eRadiofan/TMS6100-Multi-PHROM-Emulator-for-the-BBC-Micro/Firmware/Common/Src/ROMdata_TI99.c

// This is a dump of CD2325a and CD2326a combined. The index section is a binary tree!
#include "main.h"
#include "ROMdata.h"

const uint8_t phromData_TI99[DLEN_TI99] = {
  0x55, // Type: 0x55
  /* 0x0001 */  0x20, 0xb2, 0xf2, 0x4a, 0xa2, 0x20, 0x6d, 0x70, 0xad, 0x00, 0x62, 0x42, 0x8a, // Phrase 000: MORE -> 0x4642 L:0x04b6 R:0x0eb5
  /* 0x000e */  0x80, 0xb4, 0x90, 0x15, 0x00, 0x18, 0x00, 0x12, 0x3b, 0xbe, // Phrase 001: - -> 0x48dc L:0x09a8 R:0x0018
  /* 0x0018 */  0x80, 0x74, 0x00, 0x00, 0x00, 0x44, 0x00, 0x0a, 0x37, 0x3a, // Phrase 002: . -> 0x50ec R:0x0022
  /* 0x0022 */  0x80, 0x0c, 0x00, 0x00, 0x00, 0x00, 0x00, 0xc8, 0xc3, 0x62, // Phrase 003: 0 -> 0x13c3 
  /* 0x002c */  0x80, 0x8c, 0x00, 0x70, 0x00, 0x52, 0x00, 0x28, 0x90, 0xca, // Phrase 004: 1 -> 0x1409 L:0x000e R:0x004a
  /* 0x0036 */  0x80, 0x4c, 0x00, 0x00, 0x00, 0x02, 0x00, 0x28, 0x3a, 0x7c, // Phrase 005: 2 -> 0x145c R:0x0040
  /* 0x0040 */  0x80, 0xcc, 0x00, 0x00, 0x00, 0x00, 0x00, 0x28, 0x59, 0xb2, // Phrase 006: 3 -> 0x149a 
  /* 0x004a */  0x80, 0x2c, 0x00, 0x6c, 0x00, 0x2a, 0x00, 0x28, 0xe7, 0x52, // Phrase 007: 4 -> 0x14e7 L:0x0036 R:0x0054
  /* 0x0054 */  0x80, 0xac, 0x00, 0x00, 0x00, 0x7a, 0x00, 0xa8, 0x8c, 0xee, // Phrase 008: 5 -> 0x1531 R:0x005e
  /* 0x005e */  0x80, 0x6c, 0x00, 0x00, 0x00, 0x00, 0x00, 0xa8, 0x15, 0x02, // Phrase 009: 6 -> 0x15a8 
  /* 0x0068 */  0x80, 0xec, 0x00, 0x34, 0x00, 0x95, 0x00, 0xa8, 0x17, 0xf2, // Phrase 010: 7 -> 0x15e8 L:0x002c R:0x00a9
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
  0xa5, 0x4a, 0x4c, 0xd4, 0x8f, 0xde, 0x56, 0x77, 0x0d, 0xf1, 0xde, 0x7a, 0x5b, 0x42, 0xb5, 0x34,
  0x7b, 0xeb, 0x7d, 0x33, 0xe5, 0xf2, 0xf4, 0xa9, 0x57, 0x41, 0xc9, 0xab, 0x1c, 0xdb, 0x5e, 0xf7,
  0xba, 0xd7, 0xfd, 0x03, 0x00, 0x00,
  /* 0x3c4f KNOW, NO */
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
