eRadiofan/TMS6100-Multi-PHROM-Emulator-for-the-BBC-Micro/Firmware/Common/Src/ROMdata_StarWars.c

#include "main.h"
#include "ROMdata.h"

/*
0x0062,
0x019C,
0x0241,
0x02FC,
0x0436,
0x0577,
0x06C3,
0x0803,
0x08E0,
0x09D6,
0x0A59,
0x0B38,
0x0C4A,
0x0DBA,
0x0F31,
0x102E,
0x10A7,
0x11A4,
0x12C8,
0x14CD,
0x157D,
0x1747,
0x1810,
*/

#define toLE(x) x % 256, x / 256

const uint8_t phromData_StarWars[] = {
  0x00, 23, // Format type, No. of phrases: 23
  toLE(0x0030),
  toLE(0x016a),
  toLE(0x020f),
  toLE(0x02ca),
  toLE(0x0404),
  toLE(0x0545),
  toLE(0x0691),
  toLE(0x07D1),
  toLE(0x08AE),
  toLE(0x09a4),
  toLE(0x0a27),
  toLE(0x0b06),
  toLE(0x0c18),
  toLE(0x0d88),
  toLE(0x0eff),
  toLE(0x0ffc),
  toLE(0x1075),
  toLE(0x1172),
  toLE(0x1296),
  toLE(0x149b),
  toLE(0x154b),
  toLE(0x1715),
  toLE(0x17de),
  // "Use the force Luke"
  0x04, 0x00, 0x7A, 0x8A, 0x01, 0xC0, 0x4F, 0x33, 0x80, 0x68, 0x99, 0x50, 0x67, 0x8D, 0x9E, 0x95,
  0xB5, 0x5A, 0x9E, 0x8D, 0xA8, 0x86, 0x4F, 0x6E, 0x49, 0x34, 0xEE, 0x6A, 0xD1, 0xA8, 0x44, 0xC1,
  0x44, 0xB2, 0xF8, 0x92, 0x12, 0x78, 0x5F, 0x41, 0x6A, 0x4B, 0x8B, 0xEF, 0x7D, 0x27, 0x89, 0xCD,
  0x2B, 0xBE, 0x8F, 0x95, 0xA8, 0xD6, 0xAE, 0xF8, 0xDE, 0x57, 0x81, 0xD8, 0xBA, 0xE2, 0x07, 0x13,
  0x43, 0xA2, 0xED, 0x8A, 0x1F, 0xA5, 0x36, 0xBB, 0xAE, 0x2A, 0x41, 0x34, 0x66, 0x92, 0xD1, 0xB8,
  0x24, 0x55, 0xBB, 0x09, 0x5B, 0x92, 0x92, 0x4F, 0x67, 0x6A, 0xAC, 0x56, 0x0C, 0x10, 0x29, 0x8B,
  0x01, 0x0A, 0x46, 0x35, 0x40, 0x82, 0x6C, 0x0A, 0x08, 0x50, 0x98, 0x01, 0x1C, 0xB2, 0x2A, 0x80,
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
  0xD3, 0x96, 0x9A, 0xC8, 0xAC, 0x42, 0x4A, 0xDB, 0x5A, 0x24, 0xE7, 0x4A, 0x39, 0x65, 0xEB, 0x8D,
  0x42, 0x3B, 0xA4, 0xA4, 0xAD, 0x25, 0xB1, 0x48, 0x97, 0x8A, 0x80, 0x90, 0x62, 0x10, 0x10, 0x52,
  0xF6, 0x03, 0x03, 0xB4, 0xE0
};
