eRadiofan/TMS6100-Multi-PHROM-Emulator-for-the-BBC-Micro/Firmware/Common/Src/ROMdata_Acorn.c

// This is a dump of CM62024 the Acorn Speech PHROMA
#include "main.h"
#include "ROMdata.h"
/*
  PHROM Word list:

 Phrase address
 number (hex) Word

    0 0x0249  (0.125)
    1 0x0259  (0.25)
    2 0x026b  (TONE1)
    3 0x02a9  (TONE2)
    4 0x02e6  -DO
    5 0x02fd  -ED
    6 0x0327  -ING
    7 0x035f  -S
    8 0x037f  -TEEN
    9 0x03d9  -TH
   10 0x03f0  -TY
   11 0x0413  -Z
   12 0x0436  0
   13 0x04c6  00
   14 0x052d  000
   15 0x05c9  1
   16 0x0632  2
   17 0x0690  2-
   18 0x06d1  3
   19 0x073d  3-
   20 0x0787  4
   21 0x07f5  4-
   22 0x083f  5
   23 0x08b4  5-
   24 0x08e8  6
   25 0x0934  6-
   26 0x096d  7
   27 0x09c9  7-
   28 0x0a11  8
   29 0x0a44  8-
   30 0x0a70  9
   31 0x0afa  9-W
   32 0x0b5c  A
   33 0x0bb1  ACORN
   34 0x0c46  AFTER
   35 0x0cae  AGAIN
   36 0x0d40  AMOUNT
   37 0x0dbb  AN
   38 0x0e0f  AND
   39 0x0e87  ANOTHER
   40 0x0ef7  ANSWER
   41 0x0f6f  ANY
   42 0x0fc6  AVAILABLE
   43 0x1064  B
   44 0x10ba  BAD
   45 0x1134  BETWEEN
   46 0x11ad  BOTH
   47 0x11f2  BUTTON
   48 0x124c  C
   49 0x12a9  CASSETTE
   50 0x131d  CHARACTER
   51 0x1397  COMPLETE
   52 0x1403  COMPUTER
   53 0x147c  CORRECT
   54 0x14ef  D
   55 0x1537  DATA
   56 0x159b  DATE
   57 0x15e4  DO
   58 0x1624  DOLLAR
   59 0x167a  DONT
   60 0x16d3  DOWN
   61 0x1759  E
   62 0x1787  EACH
   63 0x17d0  ELEVEN
   64 0x184b  ENGAGED
   65 0x18f5  ENTER
   66 0x1957  ERROR
   67 0x19a4  ESCAPE
   68 0x1a1b  F
   69 0x1a5a  FEW
   70 0x1aa7  FILE
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
  /* 0x3f9a */  0x2d, // Z
  /* 0x3f9b */
  0x08, 0x38, 0x20, 0x4d, 0x02, 0x12, 0x08, 0xed, 0x05, 0x66, 0xee, 0x19, 0xa7, 0x34, 0x1b, 0xa8, 
  0x86, 0x55, 0xea, 0x91, 0x6c, 0x90, 0x9c, 0x9e, 0xb1, 0x4e, 0xb4, 0x71, 0x51, 0x66, 0xce, 0x3a,
  0xd1, 0xd0, 0x41, 0x65, 0x5d, 0xfb, 0x24, 0x43, 0x27, 0xb5, 0x77, 0xe3, 0x53, 0x8c, 0x10, 0x94,
  0x96, 0x8d, 0x4f, 0x35, 0x5c, 0x50, 0x46, 0xad, 0x3e, 0x4d, 0xb7, 0x41, 0x51, 0xb9, 0xe4, 0xf4,
  0xdd, 0x19, 0x67, 0xd6, 0x9c, 0x35, 0x74, 0x6d, 0x1c, 0x59, 0x8b, 0xcb, 0x38, 0xac, 0xb2, 0x69,
  0xb4, 0x36, 0x43, 0xd1, 0xcc, 0xa6, 0x53, 0x5a, 0x0c, 0x91, 0x8b, 0x56, 0xb4, 0x25, 0x33, 0x74,
  0xc5, 0xce, 0xae, 0x4e, 0xfe
  /* 0x4000 */
};
