eRadiofan/TMS6100-Multi-PHROM-Emulator-for-the-BBC-Micro/Firmware/Common/Src/ROMdata_VM61002.c

// This is a dump of VM61002 fitted in Acorn machines in the USA
#include "main.h"
#include "ROMdata.h"
/*
  PHROM Word list:

  Word or   Absolute
  word-part address
  number    (hex)    Word

  1         019E     ZERO
  2         01EB     FOUR
  3         0237     EIGHT
  4         026A     TWELVE
  5         02B3     TWENTY
  6         02FF     ONE
  7         0342     FIVE
  8         0395     NINE
  9         03ED     THIR-
  10        0425     HUNDRED
  11        047C     TWO
  12        04B3     SIX
  13        04E5     TEN
  14        051B     FIF-
  15        0541     THOUSAND
  16        05BA     THREE
  17        0606     SEVEN
  18        0650     ELEVEN
  19        06B8     TEEN-
  20        06EE     B
  21        0720     F
  22        075A     J
  23        079D     N
  24        07DD     R
  25        0809     V
  26        085D     ZEE
  27        0899     C
  28        08DB     G
  29        0919     K
  30        095A     O
  31        0988     S
  32        09B8     W
  33        0A1E     D
  34        0A52     H
  35        0A8D     L
  36        0ACC     P
  37        0B02     T
  38        0B3C     X
  39        0B75     A
  40        0BA3     E
  41        0BD9     I
  42        0C1B     M
  43        0C5A     Q
  44        0C8E     U
  45        0CCC     Y
  46        0D0E     ALPHA
  47        0D4F     ECHO
  48        0D91     DELTA
  49        0DE4     BRAVO
  50        0E41     FOXTROT
  51        0EB0     CHARLIE
  52        0F01     GOLF
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
  0x57, 0xdf, 0x54, 0x5b, 0x85, 0xbe, 0xd9, 0xe3, 0x5c, 0xc6, 0xd6, 0x6d, 0xb1, 0xa5, 0xbf, 0x99,
  0x5b, 0x3b, 0x5a, 0x30, 0x09, 0xaf, 0x2f, 0xed, 0xec, 0x31, 0xc4, 0x5c, 0xbe, 0xd6, 0x33, 0xdd,
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
};
