eRadiofan/TMS6100-Multi-PHROM-Emulator-for-the-BBC-Micro/Firmware/Common/Src/ROMdata_VM61004.c

// This is a dump of VM61004, non-indexed PHROM containing military radio phrases
#include "main.h"
#include "ROMdata.h"
/*
   PHROM Word list:

   Absolute
    address
     (hex)  Word
         0  Alpha
        64  Bravo
        BC  Charlie
       11E  Delta
       171  Echo
       1B3  Foxtrot
       248  Golf
       280  Hotel
       2F6  India
       356  Juliet
       3BC  Kilo
       409  Lima
       44C  Mike
       48E  November
       52A  Oscar
       587  Papa
       5C9  Quebec
       610  Romeo
       670  Sierra
       706  Tango
       77D  Uniform
       7FB  Victor
       86E  Whisky
       8C7  Xray
       93B  Zulu
       984  Affirmative
       A38  Negative
       ACF  Mayday
       B74  Warning
       C07  Icing
       C78  Danger
       D0B  Emergency
       DD2  Roger
       E50  Hertz
       E8D  (Pause)
       E96  Security
       F13  Target
       F6E  Vectors
       FE6  Light
      103D  Front
      1098  Way
      10DA  Glide
      115E  Open
      11C2  Lights
      1221  On
      1287  Gun dish
      130A  ArdNav
      13B9  Select
      1420  Filed
      14A5  MIG
      1511  Alert
      1579  Zone
      15FD  Terminal
      167E  Cancel
      16EB  Radios
      178E  Speed
      1800  Knots
      1868  Expect
      18D6  Action
      193C  Radio
      19AA  Power
      1A07  Path
      1A5F  Information
      1B09  True
      1B52  Pressure
      1BBF  Check
      1BF6  Decrease
      1C63  Advise
      1CED  You
      1D27  Half
      1D7E  Error
      1DDA  Call
      1E31  Wrong
      1E91  No
      1EEA  Immediately
      1FA3  Final
      200F  Please
      205A  Start
      20B6  Course
      2102  RADAR
      2181  Plan
      21EE  Target
      225B  Windows
      22F3  Watch
      2336  Use (s)
      2381  Turn
      23CE  Traffic
      2435  Tech
      248A  Slow
      24F9  Release
      256D  Key
      25A8  Ignition
      2639  Degree
      26A4  Grain
      26F9  Repair
      277C  Cancel
      2806  Verify
      28A0  Ready
      28FA  Use (z)
      2976  Out
      29BF  Other
      2A25  Oil
      2A78  Off
      2AC6  Mirror
      2B26  Rate
      2B93  Mixture
      2C16  Much
      2C6E  Rate
      2CD0  Is
      2D28  Caution
      2D97  Below
      2E13  Cylinder
      2E90  Contact
      2F0A  And
      2F51  Fuel
      2FA8  For
      2FE2  Sequence
      3068  Side
      30C3  Slow
      3119  To
      3148  Rich
      31B6  Pumps
      320C  Level
      3273  Lower
      32E5  Rear
      3364  Hold
      33C9  Long
      3435  Level
      34AE  Left
      350F  Right
      356F  Open
      35C9  Stray
      3659  Closed
      36E2  Evacuate
      379A  Failure
      3807  Service
      3881  Abort
      3902  Identify
      3999  Too low
      3A2F  Centre
      3AA9  Area
      3B09  Base
      3B45  Control
      3BBB  Measured
      3C41  The (ee)
      3C74  The (uh)
      3C95  Vacuum
      3D13  Abeam
*/

const uint8_t PHROMdata_Mil[DLEN_Milit] = {
  /* 0x0000 */
  0x63, 0xa9, 0x21, 0xb4, 0x3c, 0x16, 0xaf, 0xb6, 0x84, 0xd2, 0x0a, 0x5f, 0xb3, 0xaa, 0xe2, 0xda, 
  0x32, 0xf4, 0xcd, 0x2a, 0x93, 0xdf, 0x28, 0xd7, 0x27, 0xab, 0xc8, 0xe2, 0x5b, 0x93, 0x57, 0xaf,
  0xb2, 0xd0, 0x1b, 0x0b, 0xee, 0xb2, 0xca, 0x24, 0xae, 0xc3, 0x28, 0x4b, 0xa9, 0x0b, 0xaf, 0x0e,
  0x13, 0x47, 0x02, 0xa8, 0xa6, 0x4c, 0x00, 0x4d, 0x57, 0x08, 0xa0, 0x99, 0x0c, 0x01, 0x74, 0xed,
  0xb1, 0xea, 0x22, 0xba, 0xd4, 0xa9, 0xcd, 0xaa, 0x2b, 0xef, 0xd6, 0xe0, 0xbd, 0x6b, 0x69, 0xac,
  0x5a, 0x83, 0xf7, 0xae, 0xb3, 0xb1, 0x6a, 0x0b, 0xde, 0x32, 0xf6, 0xa2, 0x3a, 0xc2, 0x79, 0x73,
  0xbd, 0xf2, 0xfd,
  0xff,
  /* 0x0064 */
  0x02, 0x10, 0x2c, 0x34, 0xb4, 0x46, 0xaf, 0xc8, 0x8a, 0xbd, 0xd4, 0x84, 0xa9, 0xe6, 0x2d, 0xfc, 
  0x46, 0x1d, 0x7b, 0x48, 0x87, 0x2a, 0x5f, 0x55, 0x76, 0x13, 0xe9, 0xba, 0x7a, 0x97, 0xbb, 0x9c,
  0x55, 0x69, 0xa3, 0xab, 0x48, 0xd7, 0xd5, 0xb1, 0x0f, 0x63, 0xf7, 0xa1, 0xe6, 0x2a, 0x3b, 0x8e,
  0x65, 0x0c, 0xa9, 0x52, 0x55, 0x56, 0x8d, 0xb6, 0x92, 0x6a, 0x77, 0xf1, 0xbb, 0xc6, 0x86, 0xb2,
  0x3a, 0x44, 0xfd, 0x9c, 0xdb, 0x52, 0x48, 0xd7, 0x38, 0xb9, 0xef, 0x7b, 0xdd, 0xc3, 0xee, 0x7d,
  0x67, 0xb0, 0xf4, 0x89, 0x67, 0xbc, 0xfe,
  0x1f,
  /* 0x00bc */
  0x06, 0xd8, 0x2d, 0x2c, 0x01, 0x33, 0xb7, 0x67, 0xa0, 0xc5, 0xc5, 0x8d, 0xc8, 0xb2, 0xb7, 0x96, 
  0x17, 0xbf, 0x26, 0x87, 0xf9, 0x5a, 0x91, 0xf3, 0xb0, 0x1f, 0x75, 0x19, 0x45, 0xce, 0xcd, 0x71,
  0xd4, 0x65, 0x54, 0x39, 0x8e, 0xda, 0x71, 0xb6, 0xd1, 0xc5, 0x30, 0xe9, 0x6e, 0x69, 0xcb, 0x5c,
  0x51, 0x8f, 0x15, 0x66, 0x49, 0xfb, 0x80, 0x31, 0xa2, 0xe6, 0x7d, 0x9d, 0x55, 0xb6, 0x59, 0xd8,
  0xea, 0x71, 0x0f, 0xde, 0xca, 0xe5, 0x9b, 0xc7, 0xd3, 0x65, 0x92, 0x55, 0x6c, 0x2e, 0xef, 0x30,
  0x49, 0x92, 0xb1, 0x3a, 0xbd, 0xc3, 0x04, 0x72, 0xe7, 0xe6, 0xf0, 0x75, 0xeb, 0xa8, 0x93, 0xab,
  0xff,
  0x1f,
  /* 0x011e */
  0x0a, 0x28, 0x30, 0x6c, 0xad, 0xc3, 0xa7, 0xaa, 0x70, 0xd7, 0xd5, 0x76, 0x5d, 0x22, 0xee, 0x5b, 
  0x57, 0xd9, 0xf9, 0xb8, 0xa6, 0x6d, 0x59, 0x65, 0x16, 0x9b, 0xa1, 0xde, 0x7b, 0xd5, 0x99, 0x6d,
  0xa5, 0x58, 0xde, 0xd5, 0x64, 0x11, 0x5d, 0xc2, 0x69, 0xca, 0x30, 0x25, 0x5b, 0x85, 0x32, 0x21,
  0x40, 0x96, 0x26, 0x0e, 0x58, 0x4a, 0x33, 0x00, 0x4b, 0xb5, 0xad, 0xae, 0x9a, 0xf0, 0x30, 0xdf,
  0xb2, 0xc7, 0x31, 0x35, 0x55, 0xe9, 0x21, 0x5d, 0xfb, 0x34, 0xf6, 0xaa, 0xc6, 0x3c, 0xa5, 0x73,
  0x3f, 0xfe,
  0x1f,
  /* 0x0171 */
  0x2b, 0x6f, 0xb1, 0xd9, 0xd3, 0x36, 0xdf, 0xf6, 0x36, 0xb7, 0x26, 0x85, 0x08, 0xe5, 0x2e, 0x22, 
  0x1b, 0x20, 0x00, 0x25, 0xac, 0x2a, 0x20, 0xcf, 0xd3, 0x52, 0x45, 0x53, 0x6a, 0xa9, 0x9e, 0x4f,
  0x9b, 0x54, 0x47, 0xb9, 0xe4, 0xdf, 0xc3, 0x1c, 0xc6, 0x98, 0x45, 0x65, 0xbb, 0x78, 0x9f, 0xcb,
  0x5c, 0xd2, 0xea, 0x43, 0x67, 0xb0, 0xe5, 0xcd, 0x7b, 0x38, 0x9d, 0xad, 0x2c, 0x15, 0x37, 0xf1,
  0xfc,
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
}; // 149 phrases
