eRadiofan/TMS6100-Multi-PHROM-Emulator-for-the-BBC-Micro/Firmware/Common/Src/ROMdata_VM71003A.c

// This is a dump of VM71003A (female clock)
#include "main.h"
#include "ROMdata.h"
/*
Word or   Absolute
word-part address
number    (hex)    Word

1         0048     THE
2         006A     TIME
3         00F7     IS
4         015C     AM
5         0203     PM
6         0283     OH
7         02BF     O'CLOCK
8         031D     ONE
9         0383     TWO
10        03B6     THREE
11        041E     FOUR
12        047B     FIVE
13        04F9     SIX
14        052C     SEVEN
15        0584     EIGHT
16        05CB     NINE
17        063F     TEN
18        06A6     ELEVEN
19        0733     TWELVE
20        07AE     THIRTEEN
21        084E     FOURTEEN
22        08C5     FIFTEEN
23        0958     SIXTEEN
24        09F0     SEVENTEEN
25        0AAB     EIGHTEEN
26        0B46     NINETEEN
27        0C08     TWENTY
28        0C71     THIRTY
29        0CDC     FOURTY
30        0D47     FIFTY
31        0DA8     GOOD
32        0DC7     MORNING
33        0E52     AFTERNOON
34        0EF3     EVENING
35        0F6C     (0.25)
*/

const uint8_t PHROMdata_Clock[DLEN_CLOCK] = {
  0x00, 0x23, // Format type, No. of phrases: 35
  0x48, 0x00, // Phrase 000 @ 0x0048
  0x6a, 0x00, // Phrase 001 @ 0x006a
  0xf7, 0x00, // Phrase 002 @ 0x00f7
  0x5c, 0x01, // Phrase 003 @ 0x015c
  0x03, 0x02, // Phrase 004 @ 0x0203
  0x83, 0x02, // Phrase 005 @ 0x0283
  0xbf, 0x02, // Phrase 006 @ 0x02bf
  0x1d, 0x03, // Phrase 007 @ 0x031d
  0x83, 0x03, // Phrase 008 @ 0x0383
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
  0xab, 0x69, 0xda, 0x2b, 0x18, 0x9e, 0x3d, 0x37, 0x69, 0x9d, 0xa8, 0x07, 0x71, 0x9f, 0xa0, 0xbd,
  0xa2, 0x16, 0xd5, 0x7c, 0x54, 0xf6, 0x88, 0x6b, 0x54, 0x8b, 0x34, 0x49, 0x2d, 0x29, 0x49, 0x3c,
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
};
