eRadiofan/TMS6100-Multi-PHROM-Emulator-for-the-BBC-Micro/BASIC2/SPHRASE.bas

   10 REM >SPHRASE
   20
   30 PROCasm
   40 REM Reset 5220
   50 Y%=&70:CALL CMD
   60 CLS
   70 PROCPHRASE_I(15,208)
   80 PROCSETADDR(0,0)
   90 RTPE%=FNREAD
  100 PROCSETADDR(10,1)
  110 STW%=FNREAD
  120
  130 IF RTPE%=&AA THEN PRINT "PHROM ID (0,4,10,15)";
  140 IF RTPE%<>&AA AND STW%=232 THEN PRINT "PHROM ID (0,2,4,10,15)";
  150 IF RTPE%<>&AA AND STW%<>232 THEN PRINT "PHROM ID (0,2,4,15)";
  160 INPUT RN%
  170 BN% = 1
  180 IF RN% = 2 THEN BN%=0:MAX%=148:PROCINITDATA
  190 IF RN% = 0 AND RTPE%=&AA THEN PROCTI99INDEX:BN%=0:MAX%=373
  200 IF RN% = 0 AND RTPE% <> &AA THEN MAX%=206
  210 IF RN% = 10 MAX%=23
  220 IF RN% = 15 THEN BN% = 32:MAX% = 260:PRINT "Phrase Acorn = 129"
  230 IF RN% = 4 THEN MAX% = 35
  240 LAST% = 1
  250 PRINT"<RETURN> = Previous, -1 = All"
  260 REPEAT
  270   PRINT "Phrase number (1-";MAX%;")";
  280   INPUT PN%
  290   IF (PN% = 0) THEN PN% = LAST%
  300   IF PN% = -1 THEN PROCALL(RN%,BN%,MAX%-1) ELSE PROCPHRASE(RN%,BN%+PN%-1)
  310   LAST% = PN%
  320 UNTIL 0
  330
  340 DEFPROCPHRASE(RN%,PN%)
  350 AN% = -1
  360 IF RTPE%=&AA AND RN%=0 THEN AN%=IDX99%(PN%)
  370 IF RN%=2 THEN AN%=IDXDATA%(PN%)
  380 REM PRINT PN%, ~AN%
  390 IF (AN% > &4000) THEN RN%=RN%+1:AN%=AN%-&4000
  400 IF AN% >= 0 THEN PROCSETADDR(RN%,AN%):PROCSPEAK ELSE PROCPHRASE_D(RN%,PN%)
  410 ENDPROC
  420
  430 DEF PROCALL(RN%,BN%,MAX%)
  440 FOR I% = 0 TO MAX%
  450   PRINT "Phrase ";I%+1
  460   PROCPHRASE(RN%,BN%+I%)
  470   PROCWAITEOS
  480   FOR J%=0 TO 1000:NEXT
  490 NEXT
  500 ENDPROC
  510
  520 DEF FNREVERSE(A%)
  530 =USR(REVERSE) AND &FF
  540
  550 DEF FNREAD
  560 CALL RDP
  570 =?RDAT%
  580
  590 DEF PROCWAITEOS
  600 REPEAT
  610   CALL RDS
  620   STAT% = ?RDAT%
  630 UNTIL (STAT% AND &80) = 0
  640 ENDPROC
  650
  660 DEF PROCSETADDR(RN%,PA%)
  670 DTA1%?0=&40+(PA% AND &000F)
  680 DTA1%?1=&40+((PA% AND &00F0) DIV 16)
  690 DTA1%?2=&40+((PA% AND &0F00) DIV 256)
  700 DTA1%?3=&40+(RN% AND 3)*4+((PA% AND &3000) DIV &1000)
  710 DTA1%?4=&40+(RN% AND 12)/4
  720 CALL SETADDR
  730 ENDPROC
  740
  750 DEF PROCSPEAK
  760 Y%=&50:CALL CMD
  770 ENDPROC
  780
  790 DEF PROCPHRASE_D(RN%,PN%)
  800 PA%=2 * PN%
  810 PROCSETADDR(RN%,PA%)
  820 LO% = FNREVERSE(FNREAD)
  830 HI% = FNREVERSE(FNREAD)
  840 PA% = LO% + 256*HI%
  850 PROCSETADDR(RN%,PA%)
  860 PROCSPEAK
  870 ENDPROC
  880
  890 DEF PROCPHRASE_I(RN%,PN%)
  900 PA%=2 * PN%
  910 PROCSETADDR(RN%,PA%)
  920 Y%=&30:CALL CMD
  930 PROCSPEAK
  940 ENDPROC
  950
  960 DEF PROCTI99INDEX
  970 DIM IDX99%(373)
  980 PROCSETADDR(0,1)
  990 !IADR%=1
 1000 !PPTR%=0
 1010 FOR I% = 0 TO 373
 1020   CALL TIDX
 1030   IDX99%(I%)=!PPTR%
 1040 NEXT
 1050 REM Reset 5200
 1060 Y%=&78:CALL CMD
 1070 ENDPROC
 1080
 1090 DEF PROCasm
 1100 DIM CODE% 170
 1110 DIM DTA1% 5
 1120 DIM PPTR% 4
 1130 DIM IADR% 4
 1140 DIM RDAT% 1
 1150 FOR N=0 TO 2 STEP 2
 1160   P%=CODE%
 1170   [OPTN
 1180   .REVERSE STA &80
 1190   ROL &80:ROR A
 1200   ROL &80:ROR A
 1210   ROL &80:ROR A
 1220   ROL &80:ROR A
 1230   ROL &80:ROR A
 1240   ROL &80:ROR A
 1250   ROL &80:ROR A
 1260   ROL &80:ROR A
 1270   RTS
 1280   .SETADDR LDA #&9F
 1290   LDX #0
 1300   .LOOP1
 1310   LDY DTA1%,X
 1320   JSR &FFF4
 1330   INX:CPX #5
 1340   BNE LOOP1
 1350   RTS
 1360   .CMD LDA#&9F  \ Exec CMD in Y
 1370   JSR &FFF4
 1380   RTS
 1390   .RDP LDA #&9F \ Read command
 1400   LDY #&10
 1410   JSR &FFF4
 1420   .RDS          \ Return st/data
 1430   LDA #&9E
 1440   JSR &FFF4
 1450   STY RDAT%
 1460   RTS
 1470   .TIDX JSR RDP \ Get word len
 1480   TYA
 1490   CLC:ADC IADR% \ Add to pointer
 1500   BCC TIDX2
 1510   INC IADR%+1
 1520   CLC
 1530   .TIDX2 ADC #6 \ Add another 6
 1540   STA IADR%
 1550   BCC IADDR
 1560   INC IADR%+1
 1570   .IADDR:TAY    \ JMP CMD
 1580   AND #&F
 1590   ORA #&40
 1600   STA DTA1%     \ LoB Lo Nyb
 1610   TYA
 1620   LSR A:LSR A:LSR A:LSR A
 1630   ORA #&40
 1640   STA DTA1%+1   \ LoB Hi Nyb
 1650   LDA IADR%+1
 1660   TAY
 1670   AND #&F
 1680   ORA #&40
 1690   STA DTA1%+2   \ HiB Lo Nyb
 1700   TYA
 1710   LSR A:LSR A:LSR A:LSR A
 1720   ORA #&40
 1730   STA DTA1%+3   \ Hib Hi Nyb
 1740   LDA #&40
 1750   STA DTA1%+4   \ Bank 0
 1760   LDA IADR%
 1770   CLC:ADC #3    \ Inc Addr to next
 1780   STA IADR%
 1790   LDA IADR%+1
 1800   ADC #0
 1810   STA IADR%+1
 1820   JSR SETADDR   \ Go to Ptr Addr
 1830   JSR RDP:STY PPTR%+1
 1840   JSR RDP:STY PPTR%
 1850   JMP RDP       \ Go next byte
 1860   ]:NEXT:REM PRINT P%-CODE%
 1870 ENDPROC
 1880
 1890 DEF PROCINITDATA
 1900 DIM IDXDATA%(148)
 1910 IDX%=0
 1920 REPEAT
 1930   READ Y$
 1940   IDXDATA%(IDX%)=EVAL("&"+Y$)
 1950   IDX%=IDX%+1
 1960 UNTIL IDX%=148
 1970 ENDPROC
 1980
 1990 DATA 0,64,BC,11E,171,1B3,248,280
 2000 DATA 2F6,356,3BC,409,44C,48E,52A,587
 2010 DATA 5C9,610,670,706,77D,7FB,86E,8C7
 2020 DATA 93B,984,A38,ACF,B74,C07,C78,D0B
 2030 DATA DD2,E50,E8D,E96,F13,F6E,FE6,103D
 2040 DATA 1098, 10DA, 115E, 11C2, 1221, 1287, 130A, 13B9
 2050 DATA 1420, 14A5, 1511, 1579, 15FD, 167E, 16EB, 178E
 2060 DATA 1800, 1868, 18D6, 193C, 19AA, 1A07, 1A5F, 1B09
 2070 DATA 1B52, 1BBF, 1BF6, 1C63, 1CED, 1D27, 1D7E, 1DDA
 2080 DATA 1E31, 1E91, 1EEA, 1FA3, 200F, 205A, 20B6, 2102
 2090 DATA 2181, 21EE, 225B, 22F3, 2336, 2381, 23CE, 2435
 2100 DATA 248A, 24F9, 256D, 25A8, 2639, 26A4, 26F9, 277C
 2110 DATA 2806, 28A0, 28FA, 2976, 29BF, 2A25, 2A78, 2AC6
 2120 DATA 2B26, 2B93, 2C16, 2C6E, 2CD0, 2D28, 2D97, 2E13
 2130 DATA 2E90, 2F0A, 2F51, 2FA8, 2FE2, 3068, 30C3, 3119
 2140 DATA 3148, 31B6, 320C, 3273, 32E5, 3364, 33C9, 3435
 2150 DATA 34AE, 350F, 356F, 35C9, 3659, 36E2, 379A, 3807
 2160 DATA 3881, 3902, 3999, 3A2F, 3AA9, 3B09, 3B45, 3BBB
 2170 DATA 3C41, 3C74, 3C95, 3D13
