eRadiofan/TMS6100-Multi-PHROM-Emulator-for-the-BBC-Micro/Firmware/Common/Src/Interrupts.c

/*
 * Interrupts.c
 *
 *  Created: Jan 2026
 *   Author: Radiofan
 */

#include "main.h"
#ifdef STM32C051xx
#include "stm32c0xx_it.h"
#else
#include "stm32g0xx_it.h"
#endif
/******************************************************************************/
/*           Cortex-M0+ Processor Interruption and Exception Handlers          */
/******************************************************************************/

/**
  * @brief This function handles Non maskable interrupt.
  */
void NMI_Handler(void) {
  while (1) {
  }
}

/**
  * @brief This function handles Hard fault interrupt.
  */
void HardFault_Handler(void) {
  while (1) {
  }
}

/**
  * @brief This function handles System service call via SWI instruction.
  */
void SVC_Handler(void) {
}

/**
  * @brief This function handles Pendable request for system service.
  */
void PendSV_Handler(void) {
}

/**
  * @brief This function handles System tick timer.
  */
void SysTick_Handler(void) {
  HAL_IncTick();
}
