eRadiofan/TMS6100-Multi-PHROM-Emulator-for-the-BBC-Micro/Firmware/Common/Inc/ROMdata.h

/*
 * ROMdata.h
 *
 *  Created: Dec 2025
 *  Author: Radiofan
 */

//#define PHROMS_TI99

#define N_PHROMS 5

#define DLEN_ACORN 0x4000
#define DLEN_USA   0x3ede
#define DLEN_CLOCK 0x0f73
#define DLEN_Milit 0x3d96
#define DLEN_TI99  0x7ed4
#define DLEN_StarWars (0x17DE + 213)

extern const uint8_t phromData_Acorn[DLEN_ACORN];
extern const uint8_t phromData_USA[DLEN_USA];
extern const uint8_t PHROMdata_Clock[DLEN_CLOCK];
extern const uint8_t PHROMdata_Mil[DLEN_Milit];
extern const uint8_t phromData_TI99[DLEN_TI99];
extern const uint8_t phromData_StarWars[DLEN_StarWars];

typedef struct PHROM_desc {
  const unsigned char *address;
  const uint32_t rom_size;
  const uint32_t length;
} PHROM_desc;

typedef enum __attribute__((packed)) {
  RD_INIT,
  RD_ADDR,
  RD_DUMMY,
  RD_READY,
  RD_AOOB
} rd_state;

extern volatile uint8_t active;
