eRadiofan/TMS6100-Multi-PHROM-Emulator-for-the-BBC-Micro/BASIC2/SP-RAM.bas

   10 DIM SPEECH% 200
   15 I=0
   20 REPEAT
   30   READ Y
   40   SPEECH%?I=Y
   50   I=I+1
   60 UNTIL Y=0
   90 LL%=I
  100 PROCSPEAK(LL%)
  110 END
 1010 DEF PROCSPEAK(LL%)
 1015 PROCINIT
 1020 FORI=0 TO LL%-1
 1030   A%=I?SPEECH%
 1040   ARRAY%?I=USR(REVERSE) AND &FF
 1050 NEXT
 1060 ARRAY%?(LL%+1)=0
 1070 SOUND &FF60,!ARRAY% AND &FFFF,0,0
 1080 FOR I=2 TO LL% STEP 2
 1090   SOUND &FF00,ARRAY%!I AND &FFFF,0,0
 1100 NEXT
 1110 ENDPROC
 2000 DEFPROCINIT
 2010 DIM ARRAY% 200
 2020 DIM MC% 50
 2030 FOR I=0 TO 2 STEP 2
 2040   P%=MC%
 2050   [OPTI
 2060   .REVERSE STA &80
 2070   ROL &80
 2080   ROR A
 2090   ROL &80
 2100   ROR A
 2110   ROL &80
 2120   ROR A
 2130   ROL &80
 2140   ROR A
 2150   ROL &80
 2160   ROR A
 2170   ROL &80
 2180   ROR A
 2190   ROL &80
 2200   ROR A
 2210   ROL &80
 2220   ROR A
 2230   RTS
 2240   ]
 2250 NEXT
 2260 ENDPROC
 3000 DATA 69,212,4,180,85,88,85,190
 3010 DATA 129,43,17,78,53,1,241,35
 3020 DATA 44,9,85,241,34,171,194,178
 3030 DATA 211,104,204,49,109,34,196,89
 3040 DATA 59,132,229,214,181,6,20,193
 3050 DATA 57,121,174,65,150,72,46,77
 3060 DATA 139,143,225,46,85,145,98,228
 3070 DATA 24,108,156,58,232,185,6,21
 3080 DATA 73,44,218,45,69,101,83,75
 3090 DATA 190,139,17,206,109,79,21,105
 3100 DATA 96,179,193,178,196,186,237,52
 3110 DATA 240,46,207,19,59,81,58,149
 3120 DATA 37,220,170,213,206,167,71,92
 3130 DATA 35,182,52,146,209,188,246,169
 3140 DATA 141,30,178,235,30,41,101,38
 3150 DATA 195,204,71,74,89,73,177,16
 3160 DATA 207,210,134,82,140,59,29,100
 3170 DATA 221,164,160,238,169,94,47,0
